afonsus1997/Arktika-FPGA/Hardware/arktika-fpga/Media/arktikaFPGA.bmp

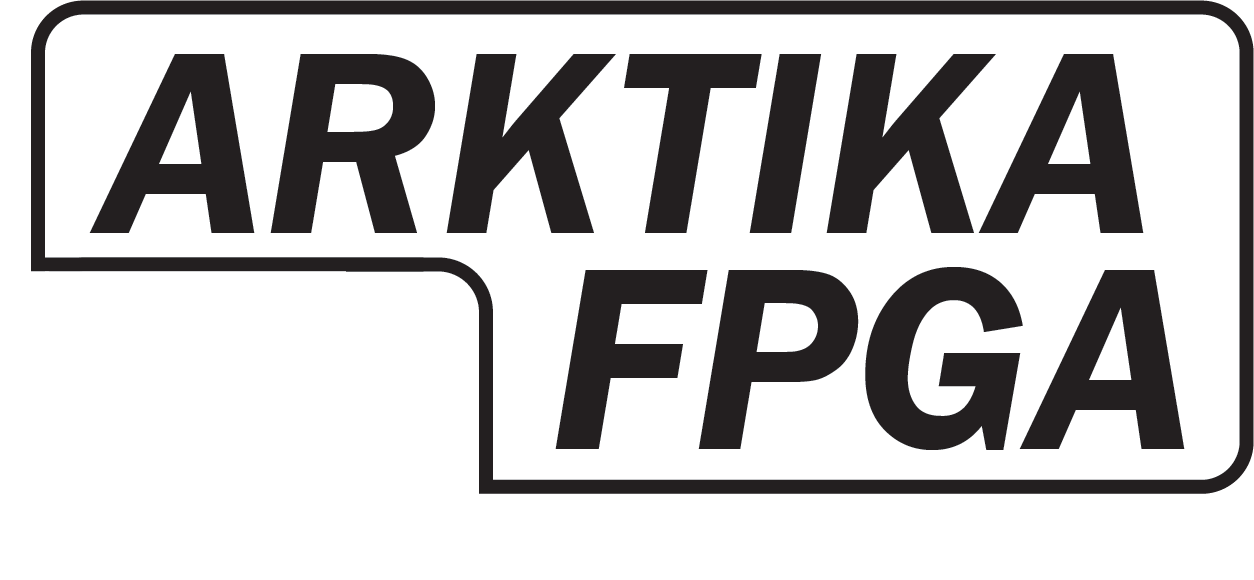
Hardware/arktika-fpga/Media/arktikaFPGA.bmp
